kpzip/PICalculator/Emulator/src/pic16register.cpp

/*
 * pic16register.cpp
 *
 *  Created on: Jan 23, 2025
 *      Author: max
 */

#include "pic16register.h"

template <class Machine>
uint8_t PIC16PointerRegister<Machine>::read(Machine *machine) {
	return 0;
}

template <class Machine>
void PIC16PointerRegister<Machine>::write(Machine *machine, uint8_t val) {

}
