kpzip/PICalculator/programs/fpu/STM/src/gui/mod.rs

use stm32f4xx_hal::gpio::Pin;
use stm32f4xx_hal::hal::digital::OutputPin;
use sci_error::SciErrorState;
use sci_mode::SciModeState;
use stm32f4xx_hal::spi::{Instance, SpiSlave};
use crate::gui::constants::ConstantsState;
use crate::gui::graph::GraphState;
use crate::gui::graph_eq::GraphEqState;

pub mod sci_error;
pub mod sci_mode;
mod graph_eq;
mod graph;
mod constants;

// 128 px wide by 64 px tall
pub const DISPLAY_WIDTH: usize = 128;
pub const DISPLAY_HEIGHT: usize = 64;

// 16 chars horizontally by 4 lines
pub const DISPLAY_TEXT_WIDTH: usize = 16;
pub const DISPLAY_TEXT_HEIGHT: usize = 4;

#[derive(Clone, Copy)]
pub enum CalculatorMenu {
    Sci,
    SciError,
    GraphEq,
    Graph,
    Constants,
}

pub struct CalculatorState {
    pub second: bool,
    pub alpha: bool,
    pub degrees: bool,
    pub mode: CalculatorMenu,
    pub sci_state: SciModeState,
    pub sci_err_state: SciErrorState,
    pub graph_eq_state: GraphEqState,
    pub graph_state: GraphState,
    pub constants_state: ConstantsState,
}

impl CalculatorState {
    pub fn new() -> Self {
        Self {
            second: false,
            alpha: false,
            degrees: false,
            mode: CalculatorMenu::Sci,
            sci_state: SciModeState::new(),
            sci_err_state: SciErrorState::new(),
            graph_eq_state: GraphEqState::new(),
            graph_state: GraphState::new(),
            constants_state: ConstantsState::new(),
        }
    }
}

pub fn handle_button_press(key_id: u8, calc_state: &mut CalculatorState) {
    match key_id {
        24 => {
            // Alpha
            calc_state.alpha = !calc_state.alpha;
        }
        30 => {
            // Second
            calc_state.second = !calc_state.second;
        }
        12 => {
            // Degrees / Radians
            if !calc_state.second {
                calc_state.degrees = true;
            } else {
                calc_state.degrees = false;
            }
        }
        _ => {
            // Do nothing
        }
    }
    match calc_state.mode {
        CalculatorMenu::Sci => {
            sci_mode::handle_button_press(key_id, calc_state)
        }
        CalculatorMenu::SciError => {
            sci_error::handle_button_press(key_id, calc_state)
        }
        CalculatorMenu::GraphEq => {
            graph_eq::handle_button_press(key_id, calc_state)
        }
        CalculatorMenu::Graph => {
            graph::handle_button_press(key_id, calc_state)
        }
        CalculatorMenu::Constants => {
            constants::handle_button_press(key_id, calc_state)
        }
        _ => unimplemented!(),
    }
}

pub fn update_gui<SPI: Instance, MODE, const L: char, const N: u8>(
    state: &mut CalculatorState,
    spi: &mut SpiSlave<SPI>,
    ready: &mut Pin<L, N, MODE>,
) where
    Pin<L, N, MODE>: OutputPin
{
    match state.mode {
        CalculatorMenu::Sci => {
            sci_mode::update_gui(state, spi, ready)
        }
        CalculatorMenu::SciError => {
            sci_error::update_gui(state, spi, ready)
        }
        CalculatorMenu::GraphEq => {
            graph_eq::update_gui(state, spi, ready)
        }
        CalculatorMenu::Graph => {
            graph::update_gui(state, spi, ready)
        }
        CalculatorMenu::Constants => {
            constants::update_gui(state, spi, ready)
        }
        _ => unimplemented!(),
    }
}

#[inline]
pub fn get_cursor_index(mut row: u8, mut col: u8) -> u8 {
    col = (col & 0x0F) / 2;
    row = row & 0x03;

    let mut data = 0x80 | ((row & 0x01) << 4);
    data |= (row & 0x02) << 2;
    data |= col;
    data
}

#[inline]
pub fn clear_gdram<SPI: Instance>(spi: &mut SpiSlave<SPI>) {
    for i in 0..32u8 {
        spi.write(&[0x81, 0x80 | i]).unwrap();
        spi.write(&[0x81, 0x80]).unwrap();
        for i in 0..16u8 {
            spi.write(&[0x82, 0x00]).unwrap();
            spi.write(&[0x82, 0x00]).unwrap();
        }
    }
}
